Alex-2-Graf/Leningrad-2-128k-SRAM/Sources/2 AY-128K схема.jpg

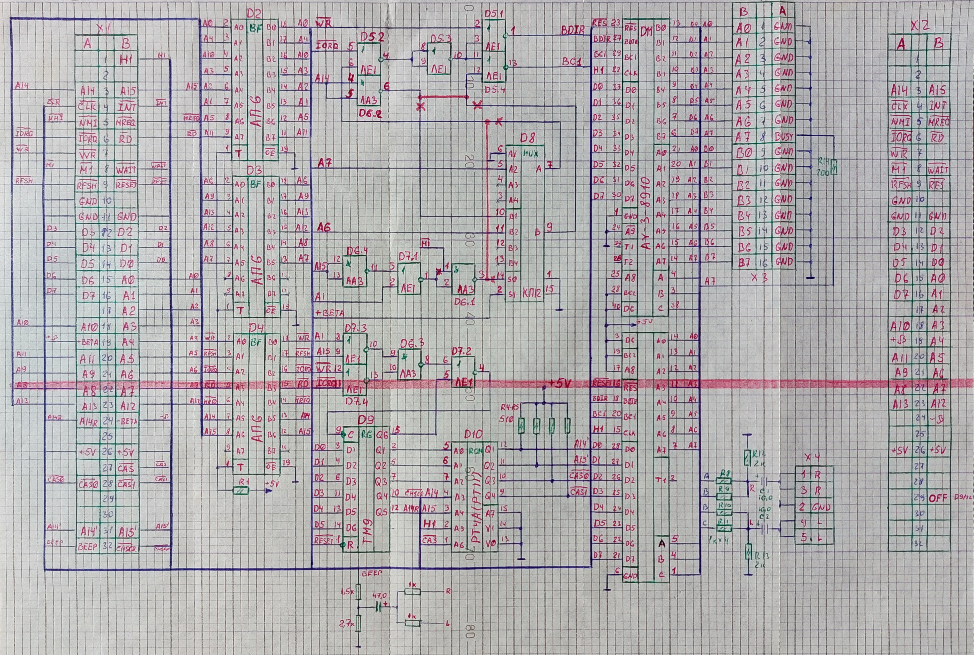
Sources/2 AY-128K схема.jpg
