Alex-2-Graf/Leningrad-2-128k-SRAM/Sources/rlvk971125.png

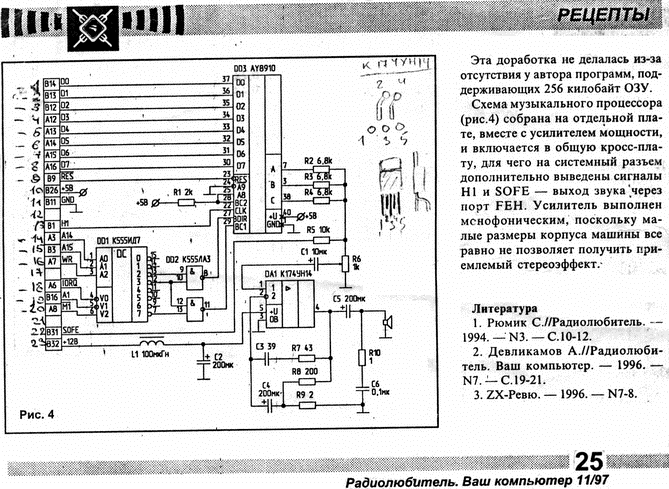
Sources/rlvk971125.png
