Alex-2-Graf/Leningrad-2-128k-SRAM/VGA/VGA 1.jpg

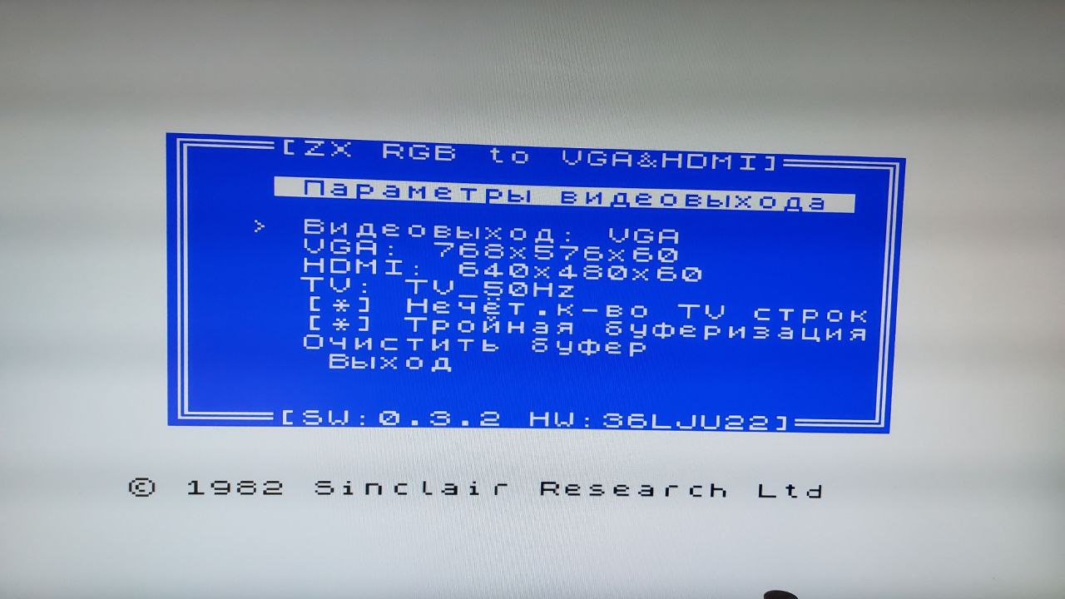
VGA/VGA 1.jpg
